theparanoids/keyhole-badge/final-artefacts/jig/pdf/badge_jig-B_Cu.pdf

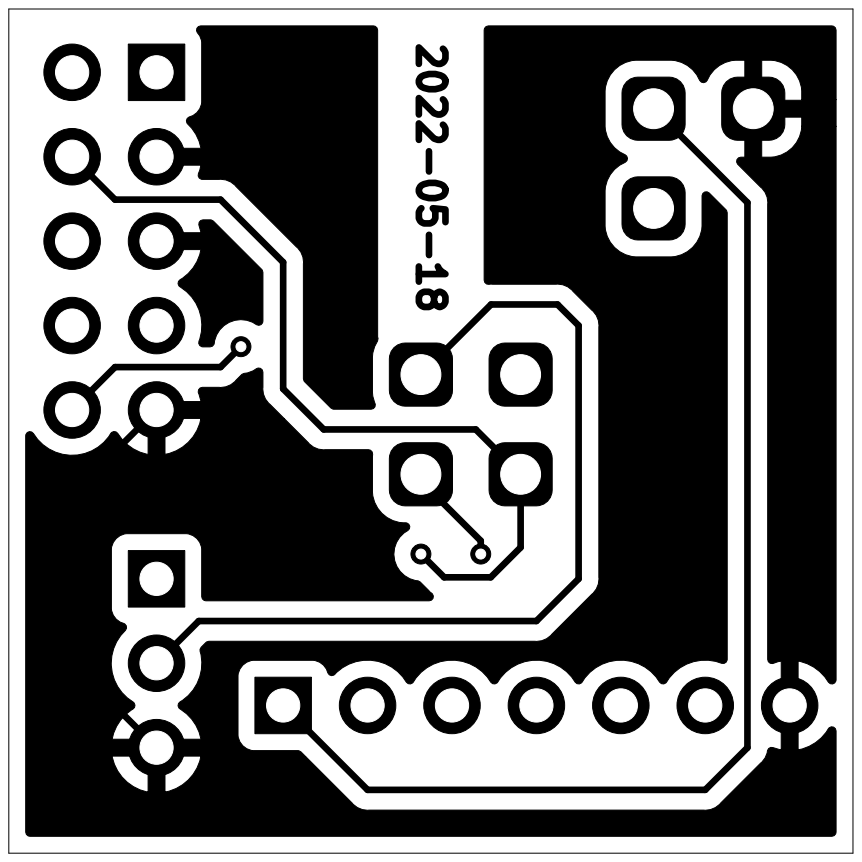
[picture p11: page 1]

Copyright Yahoo, Licensed under the terms of the Apache-2.0 license. 2022-05-18

File: badge_jig.kicad_pcb Sheet: Yahoo See LICENSE file in project root for terms.

Id: 1/1 Title: Paranoids Badge Programming Jig
